virmos/fgpa_tetris/01_Hack1-minimal/ALU/ALU.png

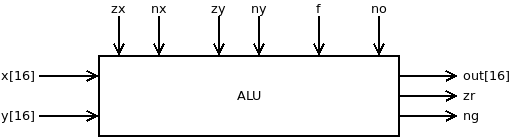
01_Hack1-minimal/ALU/ALU.png
