virmos/fgpa_tetris/01_Hack1-minimal/ALU/ALU_tb.png

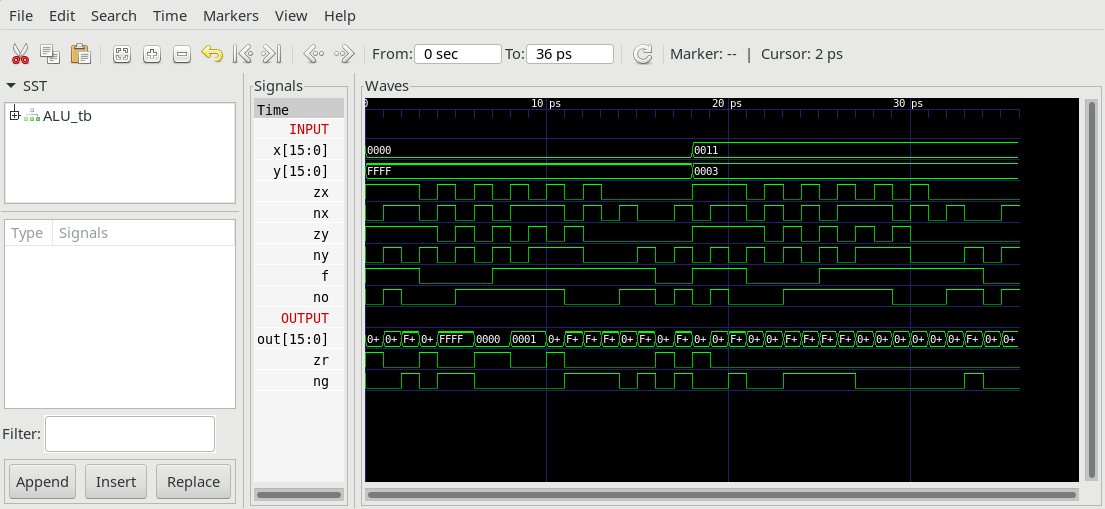
01_Hack1-minimal/ALU/ALU_tb.png
