virmos/fgpa_tetris/01_Hack1-minimal/Clock/Clock_tb.png

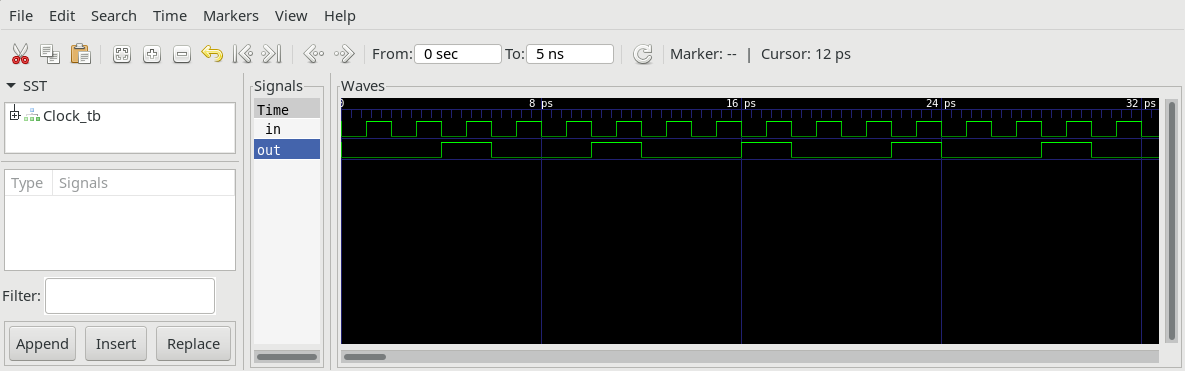
01_Hack1-minimal/Clock/Clock_tb.png
