virmos/fgpa_tetris/01_Hack1-minimal/CPU/CPU.png

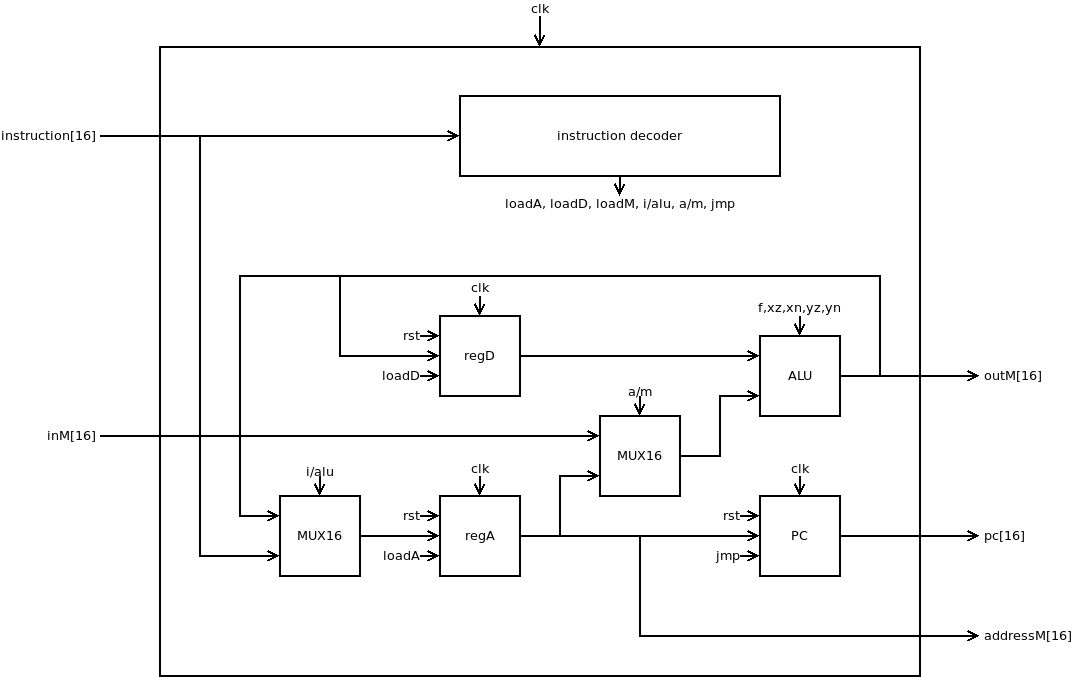
01_Hack1-minimal/CPU/CPU.png
