virmos/fgpa_tetris/01_Hack1-minimal/CPU/CPU_tb.png

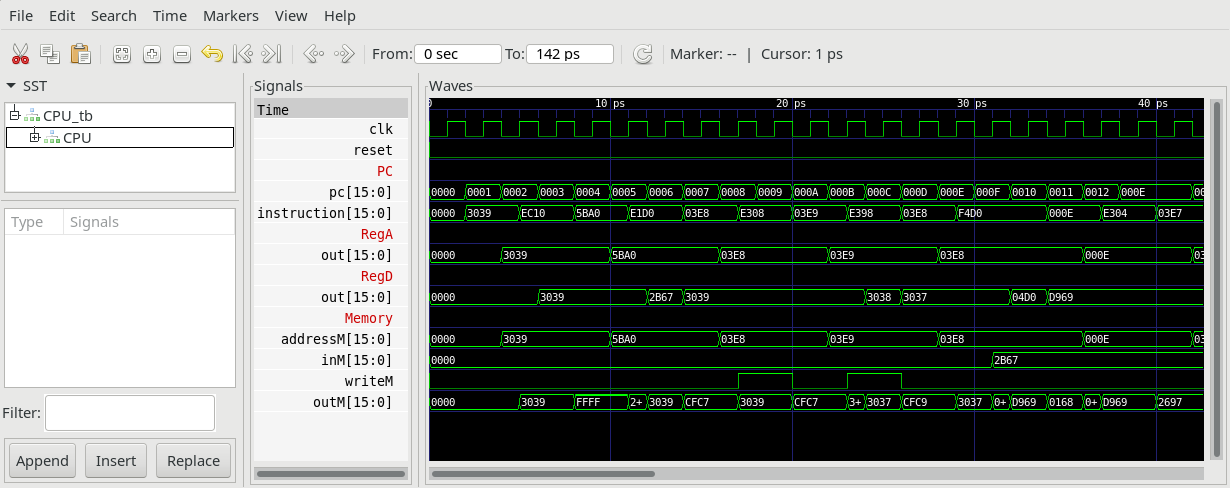
01_Hack1-minimal/CPU/CPU_tb.png
