virmos/fgpa_tetris/01_Hack1-minimal/Hack1/Hack1.png

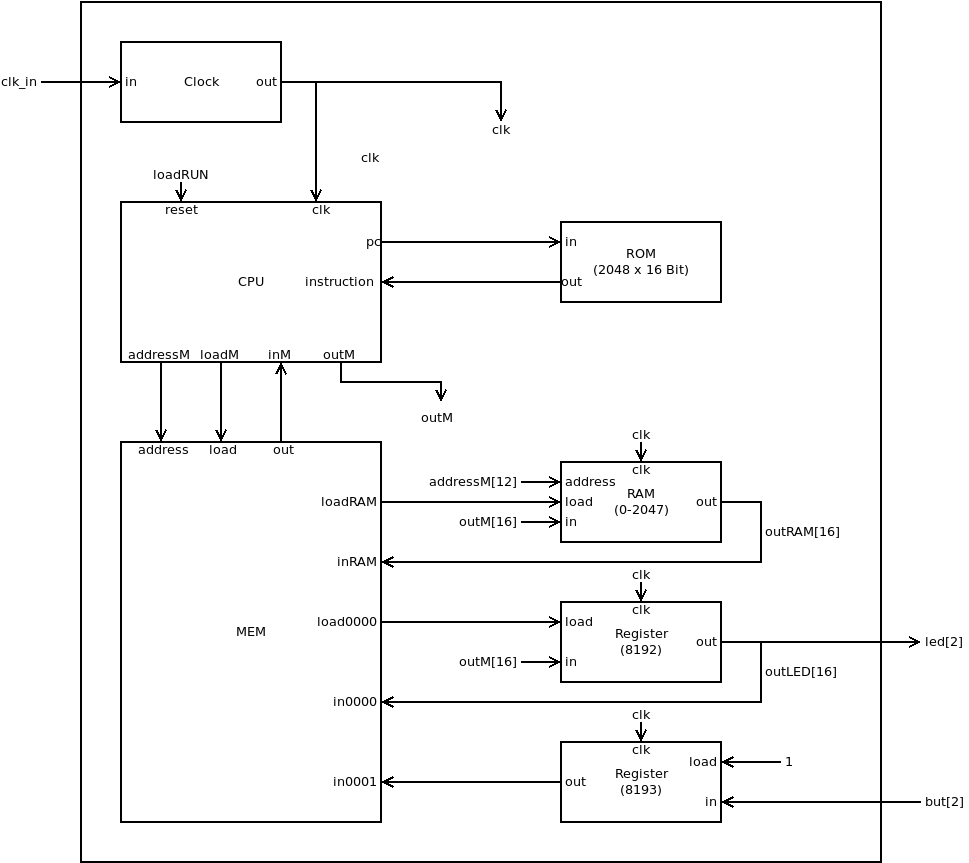
01_Hack1-minimal/Hack1/Hack1.png
