virmos/fgpa_tetris/01_Hack1-minimal/Hack1/Hack1_tb.png

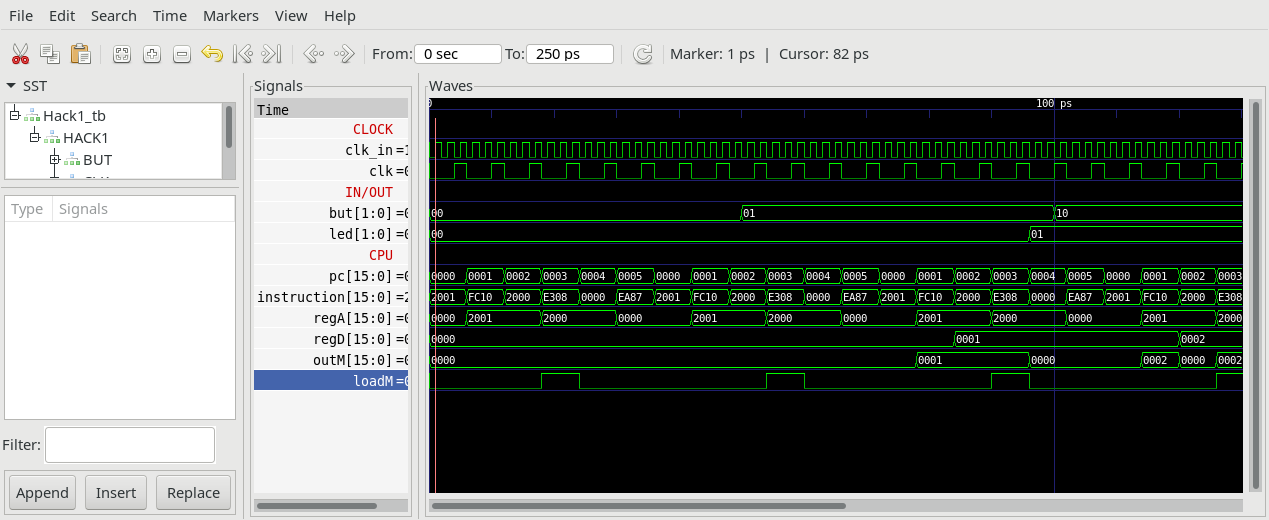
01_Hack1-minimal/Hack1/Hack1_tb.png
