virmos/fgpa_tetris/01_Hack1-minimal/Memory/Memory.png

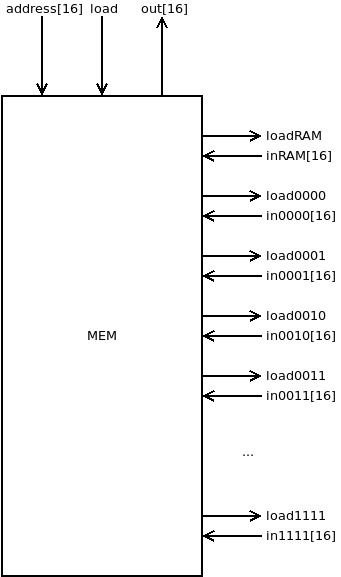
01_Hack1-minimal/Memory/Memory.png
