virmos/fgpa_tetris/01_Hack1-minimal/Memory/Memory_tb.png

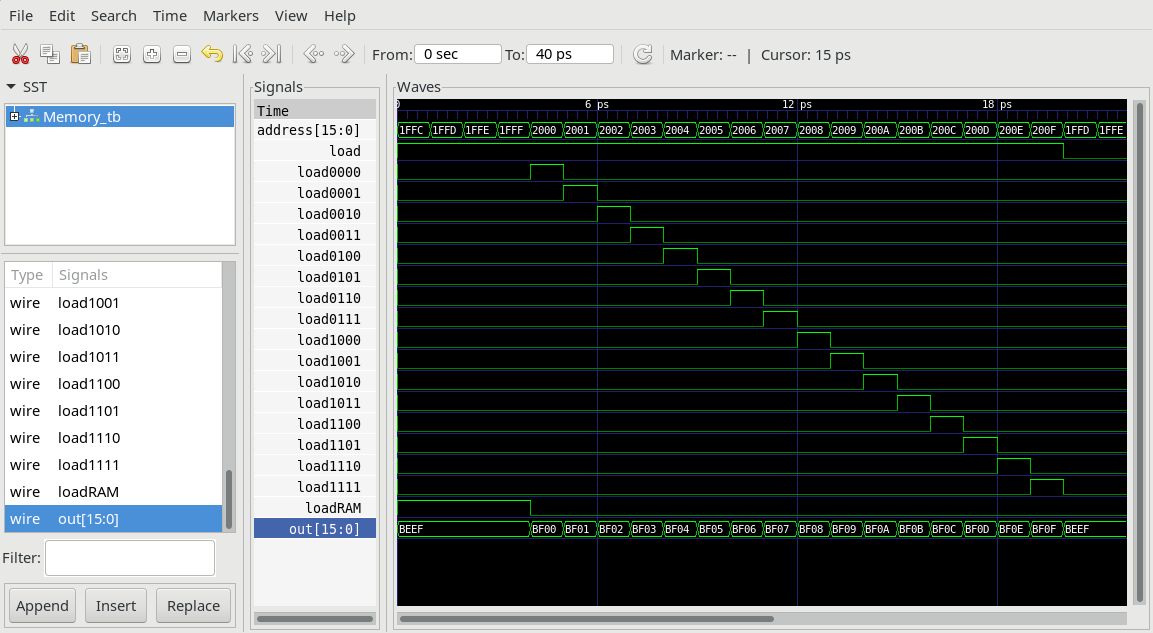
01_Hack1-minimal/Memory/Memory_tb.png
