virmos/fgpa_tetris/01_Hack1-minimal/PC/PC.png

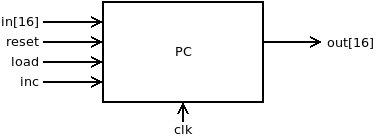
01_Hack1-minimal/PC/PC.png
