virmos/fgpa_tetris/01_Hack1-minimal/PC/PC_tb.png

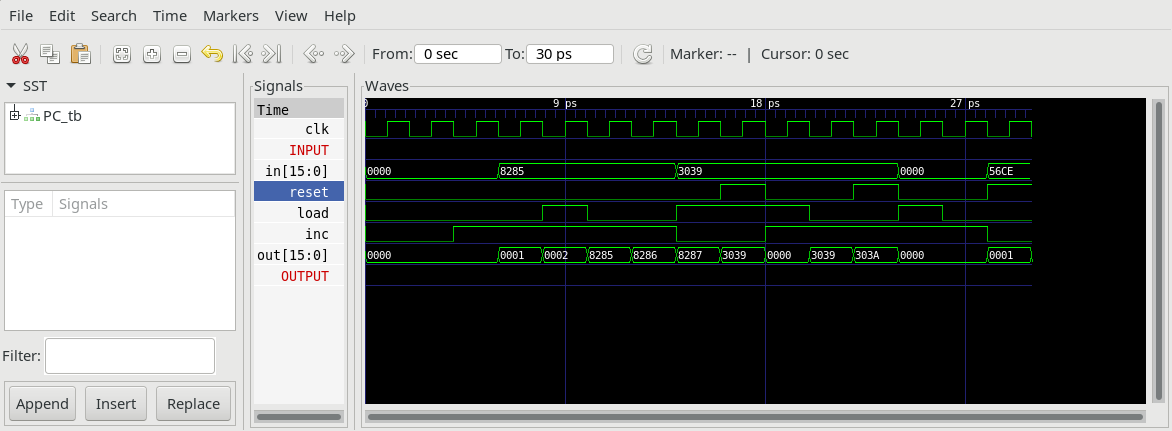
01_Hack1-minimal/PC/PC_tb.png
