virmos/fgpa_tetris/02_Hack2-UART/Hack2/Hack2_tb.png

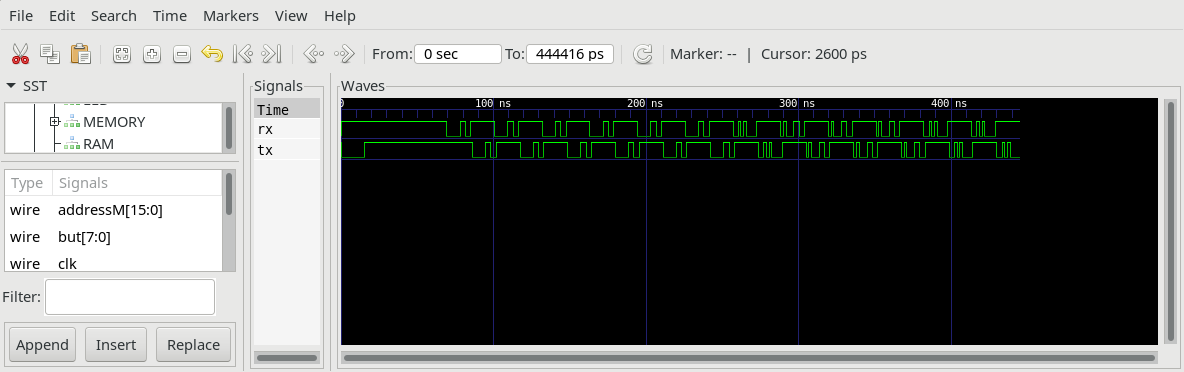
02_Hack2-UART/Hack2/Hack2_tb.png
