virmos/fgpa_tetris/02_Hack2-UART/ShifterR/ShifterR_tb.png

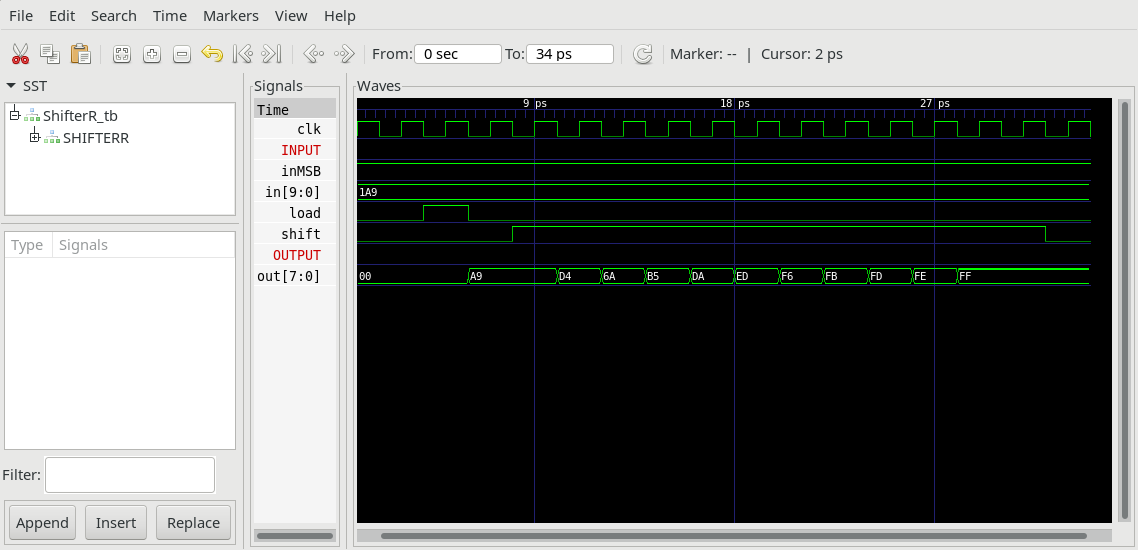
02_Hack2-UART/ShifterR/ShifterR_tb.png
