virmos/fgpa_tetris/02_Hack2-UART/Switch/Switch_tb.png

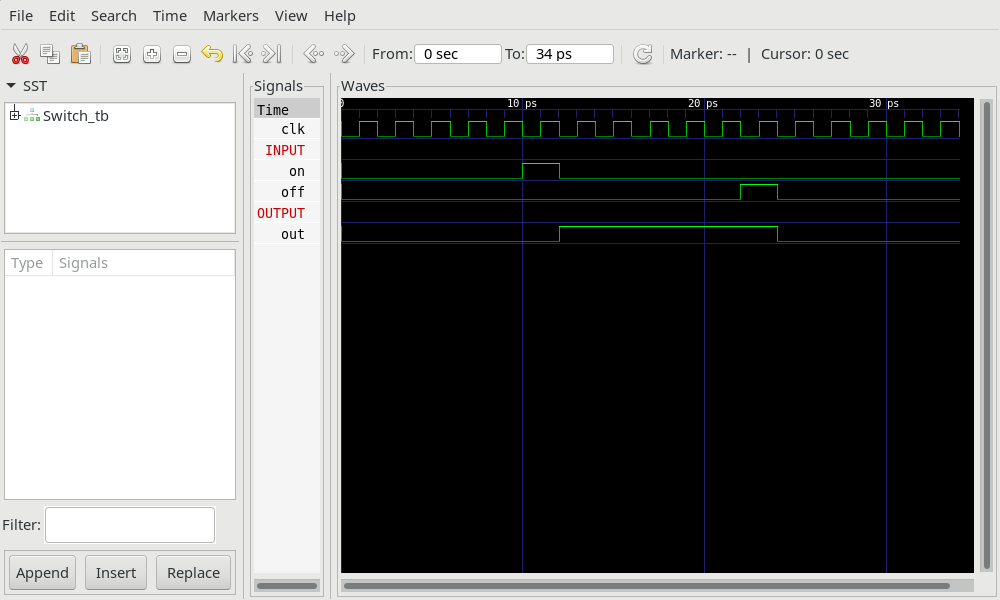
02_Hack2-UART/Switch/Switch_tb.png
