virmos/fgpa_tetris/02_Hack2-UART/UartRX/UartRX.png

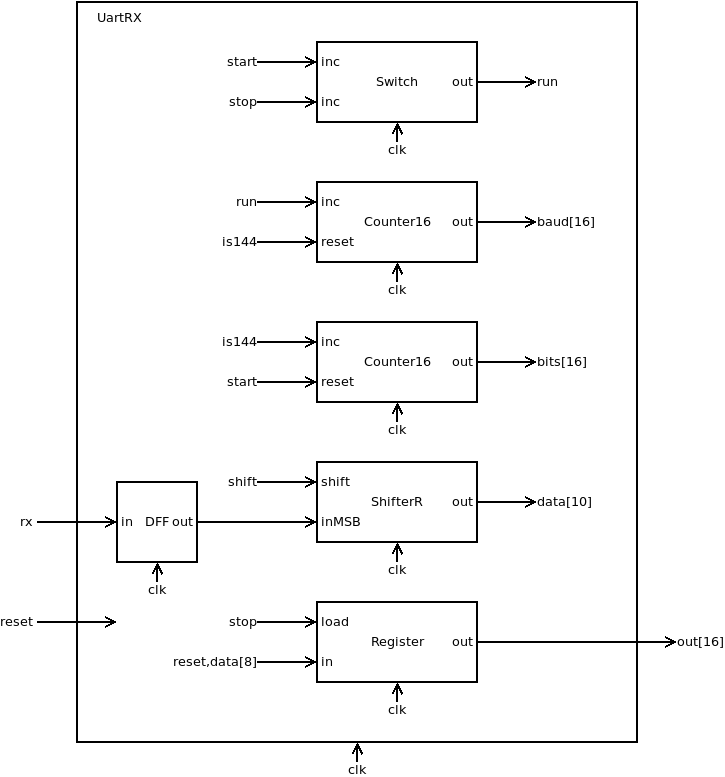
02_Hack2-UART/UartRX/UartRX.png
