virmos/fgpa_tetris/02_Hack2-UART/UartRX/UartRX_tb.png

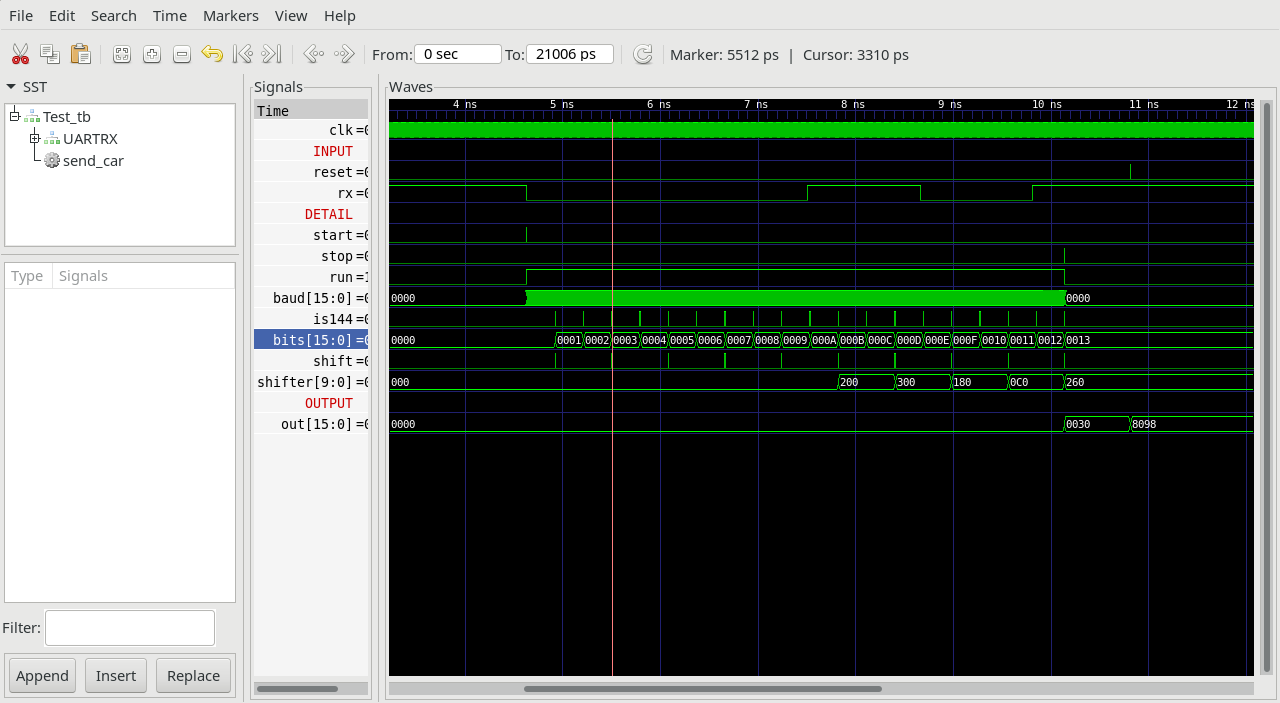
02_Hack2-UART/UartRX/UartRX_tb.png
