virmos/fgpa_tetris/02_Hack2-UART/UartTX/UartTX.png

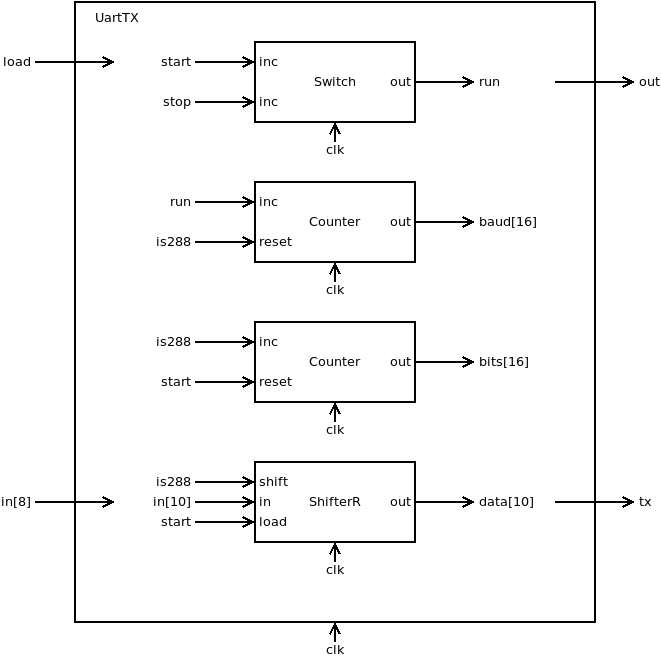
02_Hack2-UART/UartTX/UartTX.png
