virmos/fgpa_tetris/02_Hack2-UART/UartTX/UartTX_tb.png

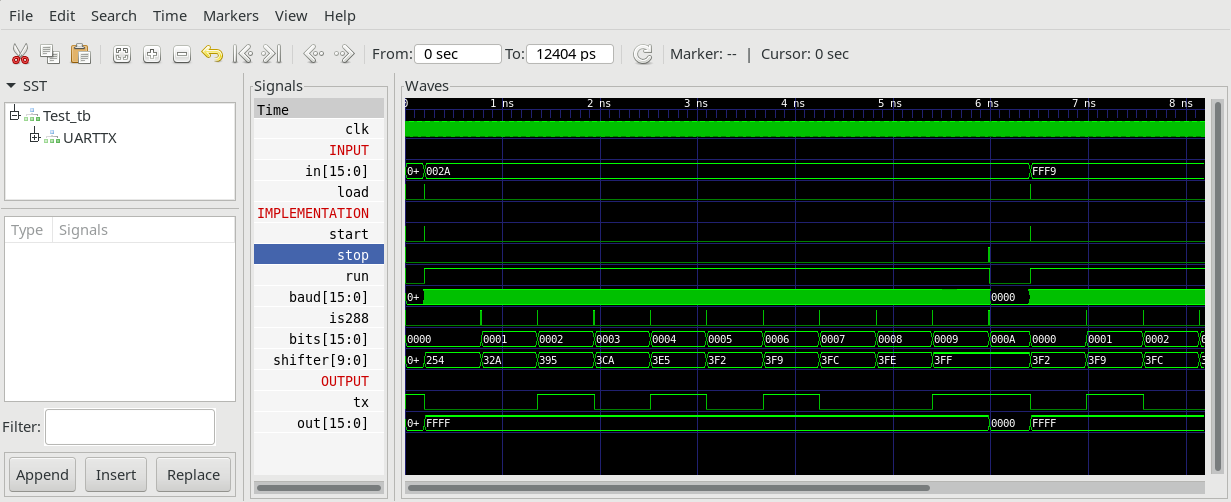
02_Hack2-UART/UartTX/UartTX_tb.png
