virmos/fgpa_tetris/03_Hack3-SRAM/Hack3/Hack3.png

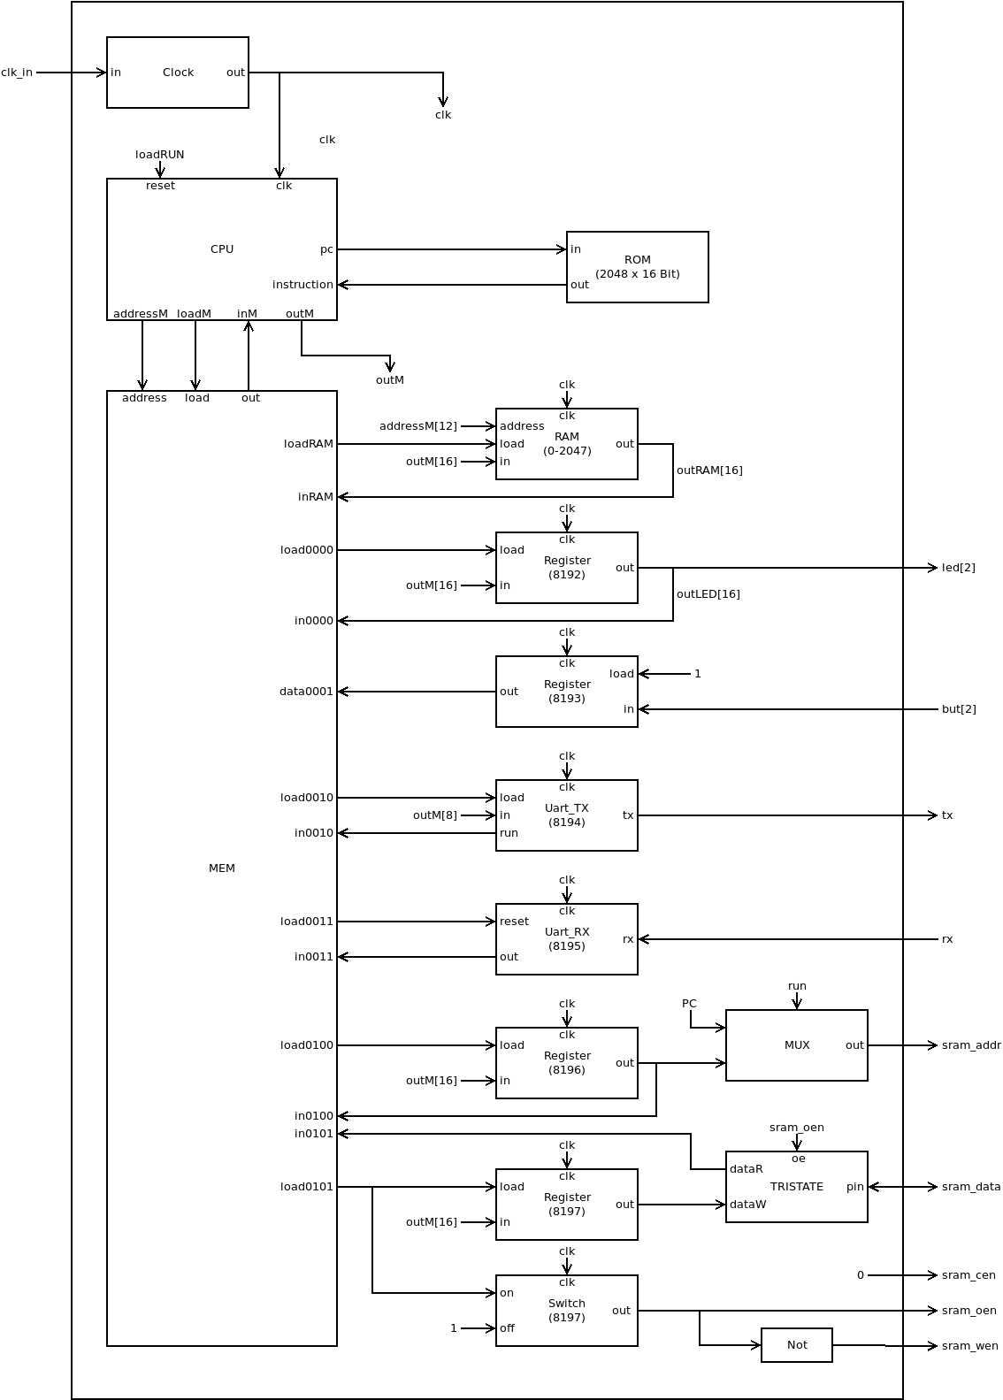
03_Hack3-SRAM/Hack3/Hack3.png
