virmos/fgpa_tetris/03_Hack3-SRAM/Hack3/Hack3_tb.png

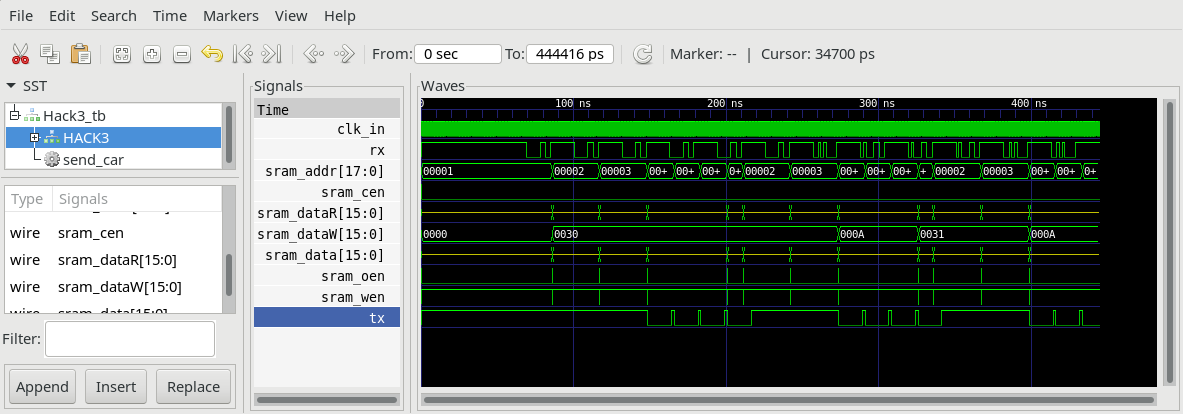
03_Hack3-SRAM/Hack3/Hack3_tb.png
