virmos/fgpa_tetris/04_Hack4-BOOT/doc/boot.png

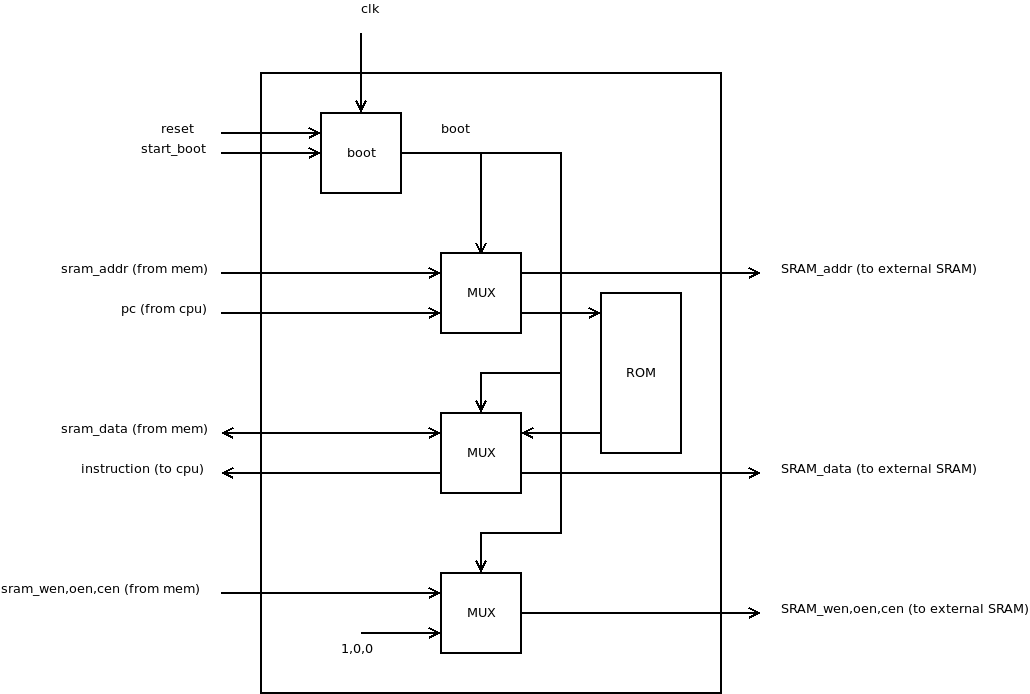
04_Hack4-BOOT/doc/boot.png
