virmos/fgpa_tetris/04_Hack4-BOOT/doc/bootloader.png

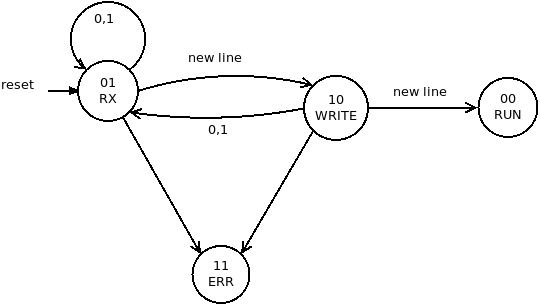
04_Hack4-BOOT/doc/bootloader.png
