virmos/fgpa_tetris/04_Hack4-BOOT/doc/hack-4.png

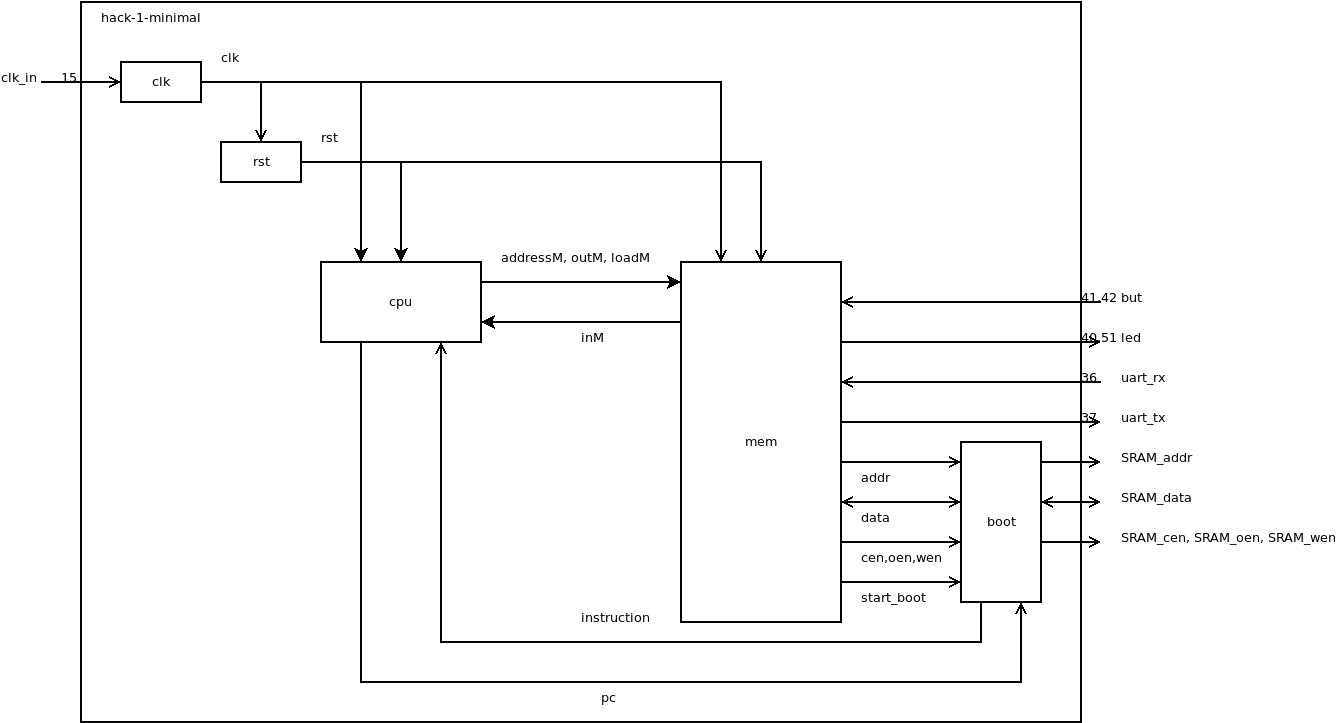
04_Hack4-BOOT/doc/hack-4.png
