virmos/fgpa_tetris/04_Hack4-BOOT/Hack4/Hack4.png

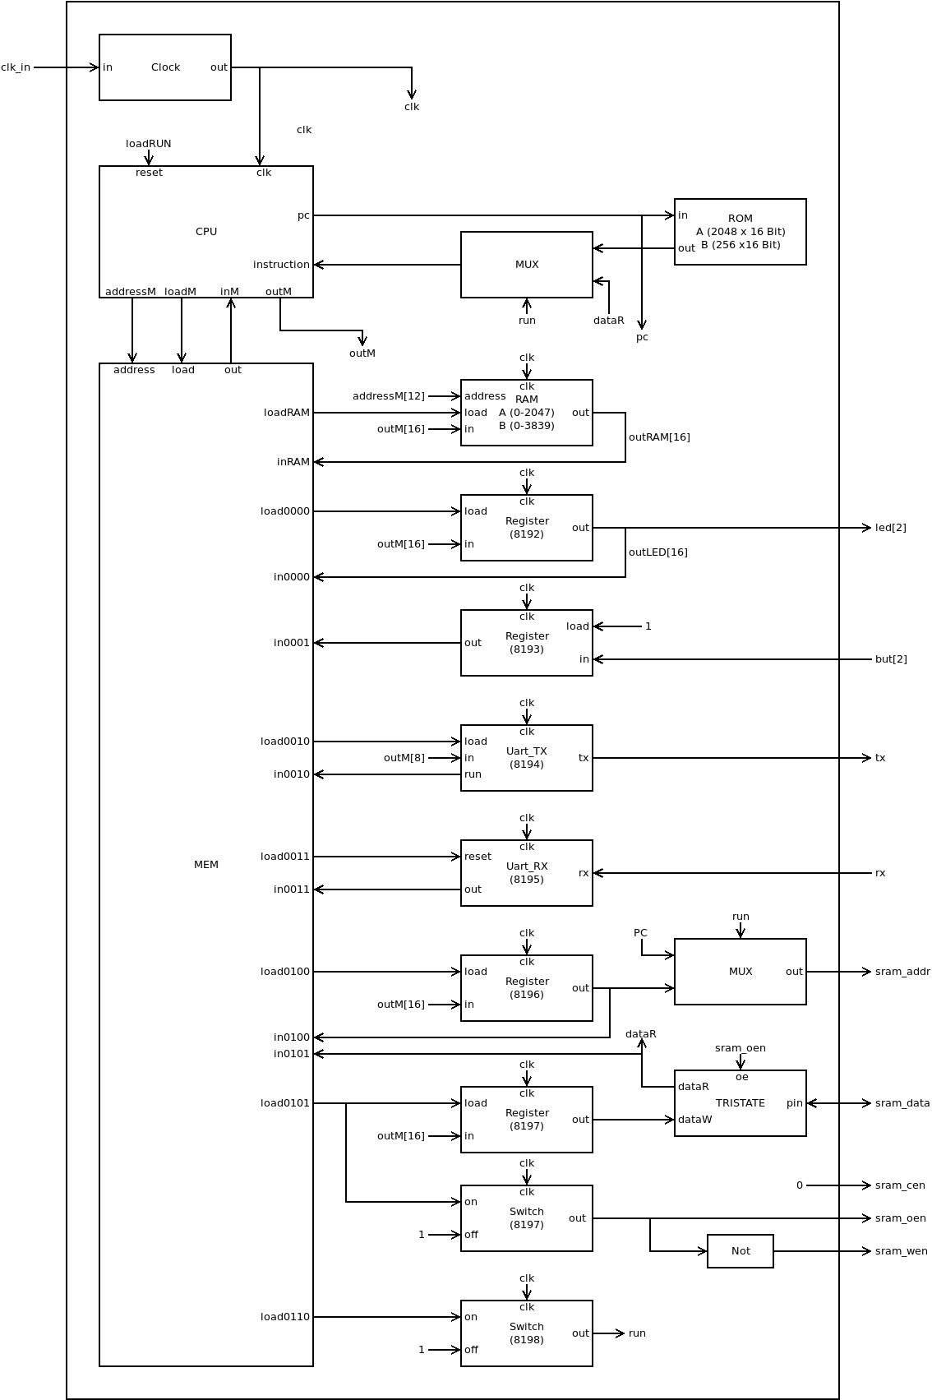
04_Hack4-BOOT/Hack4/Hack4.png
