virmos/fgpa_tetris/05_Jack-OS/Average/average.JPG

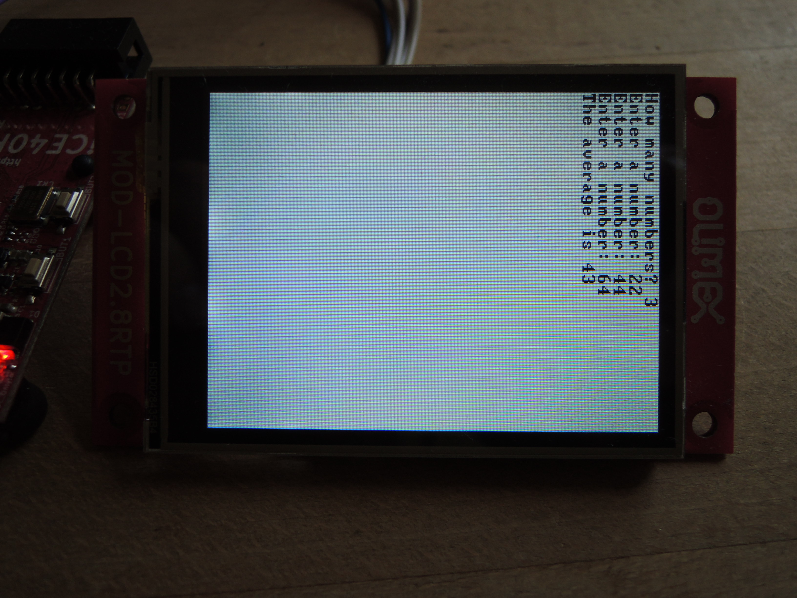
05_Jack-OS/Average/average.JPG
