virmos/fgpa_tetris/06_Hack6-LCD/Hack6/Hack6_tb.png

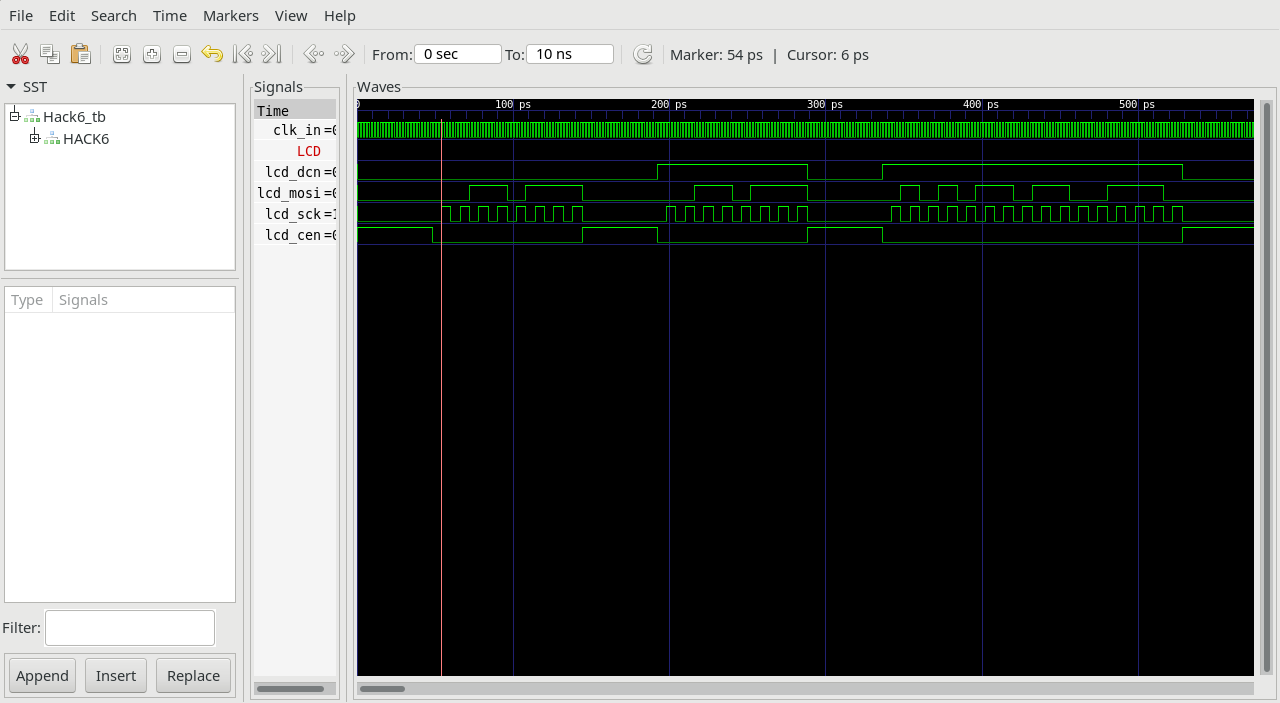
06_Hack6-LCD/Hack6/Hack6_tb.png
