virmos/fgpa_tetris/06_Hack6-LCD/Hack6/Hack.png

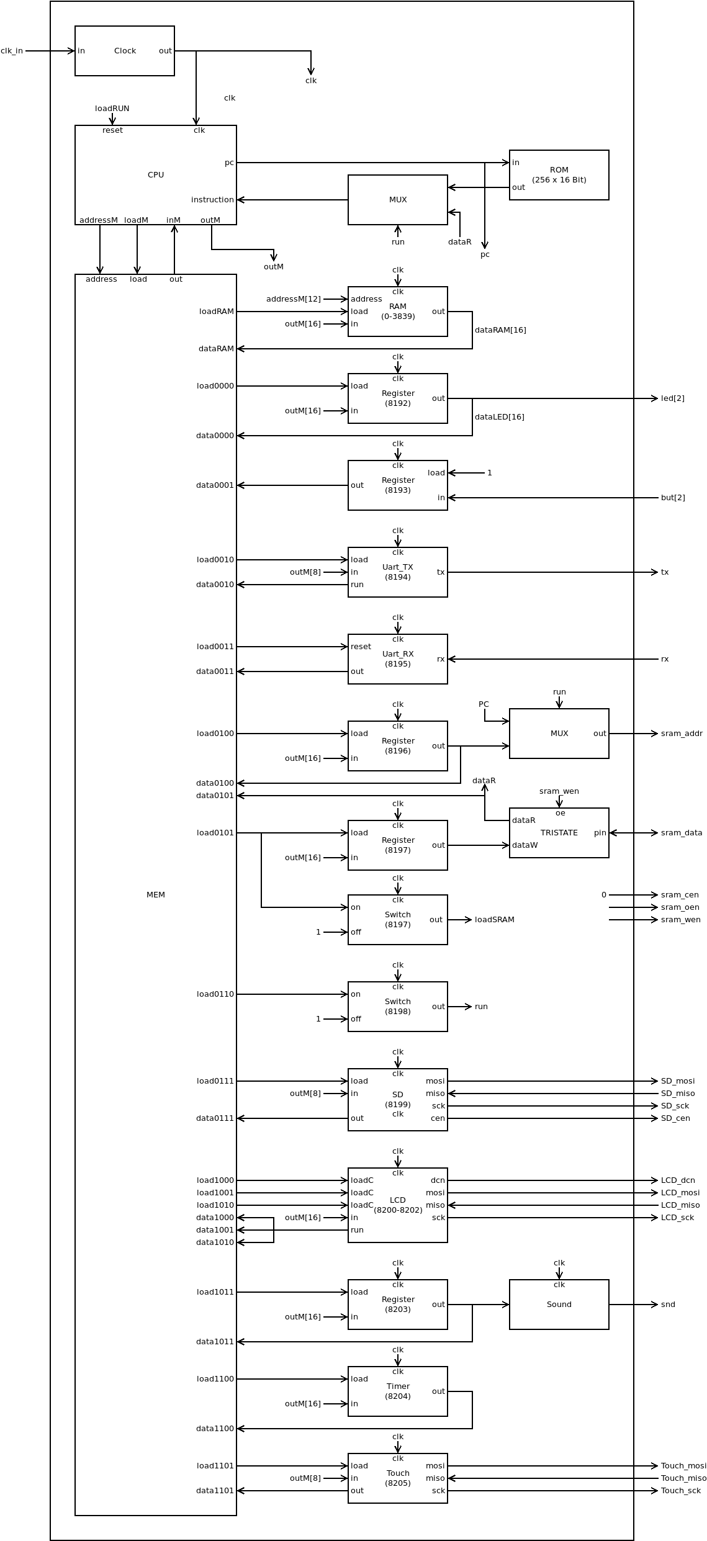
06_Hack6-LCD/Hack6/Hack.png
