virmos/fgpa_tetris/06_Hack6-LCD/jack/Pong/pong.jpg

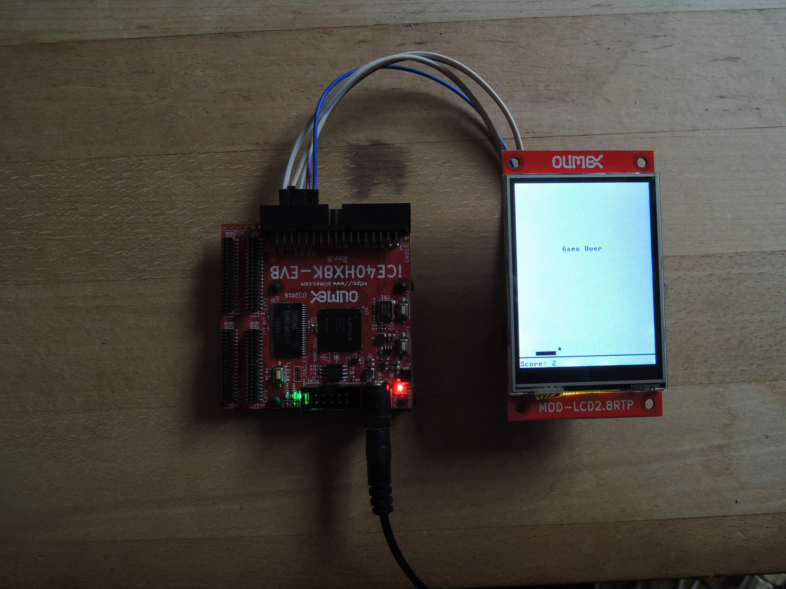
06_Hack6-LCD/jack/Pong/pong.jpg
