virmos/fgpa_tetris/06_Hack6-LCD/LCD/LCD.png

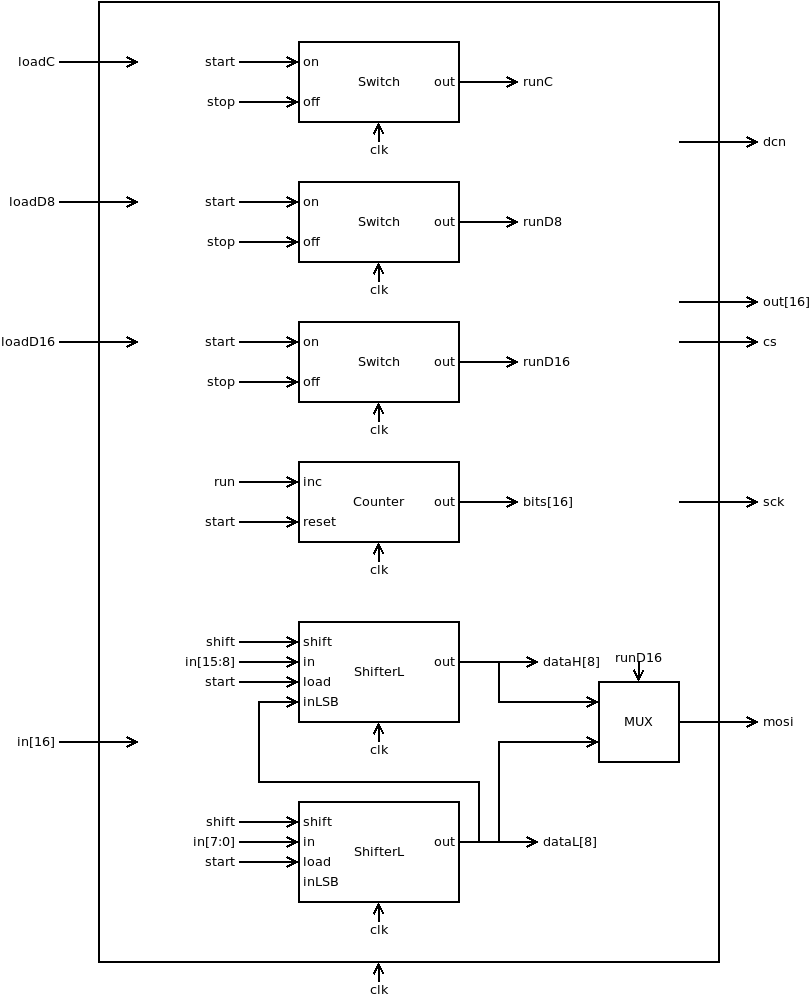
06_Hack6-LCD/LCD/LCD.png
