virmos/fgpa_tetris/06_Hack6-LCD/LCD/LCD_tb.png

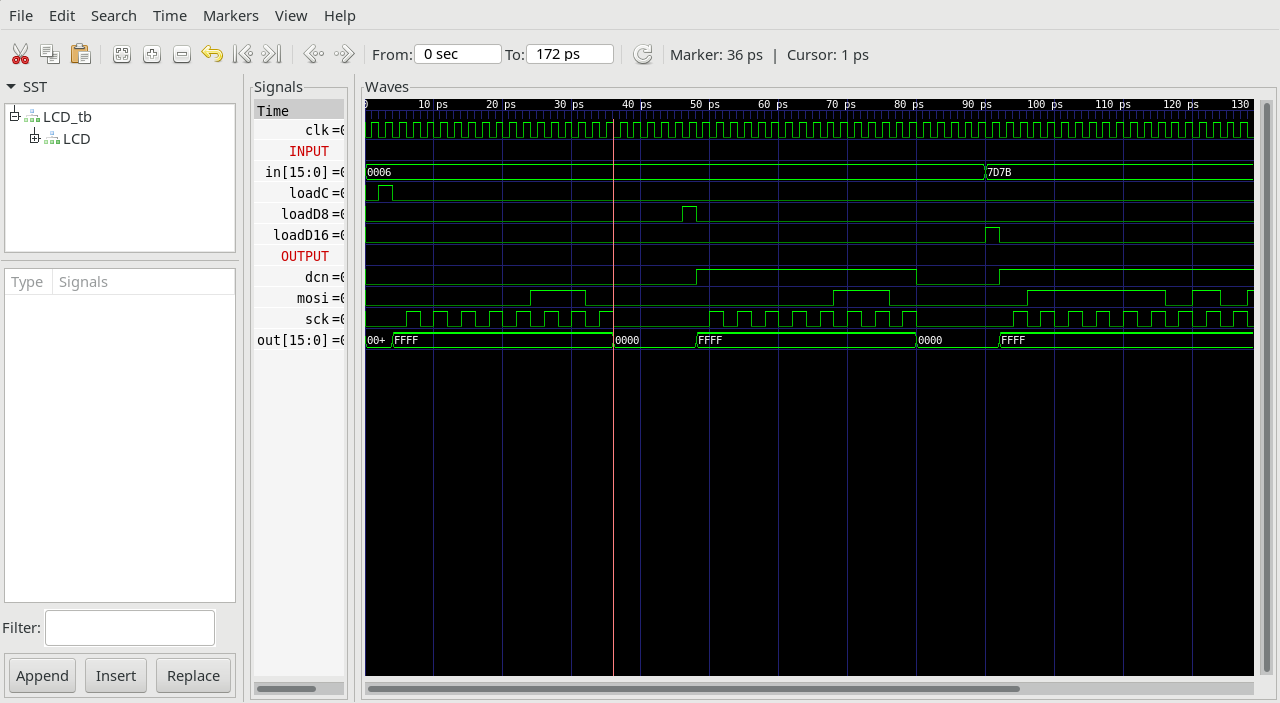
06_Hack6-LCD/LCD/LCD_tb.png
