virmos/fgpa_tetris/06_Hack6-LCD/ShifterL/ShifterL_tb.png

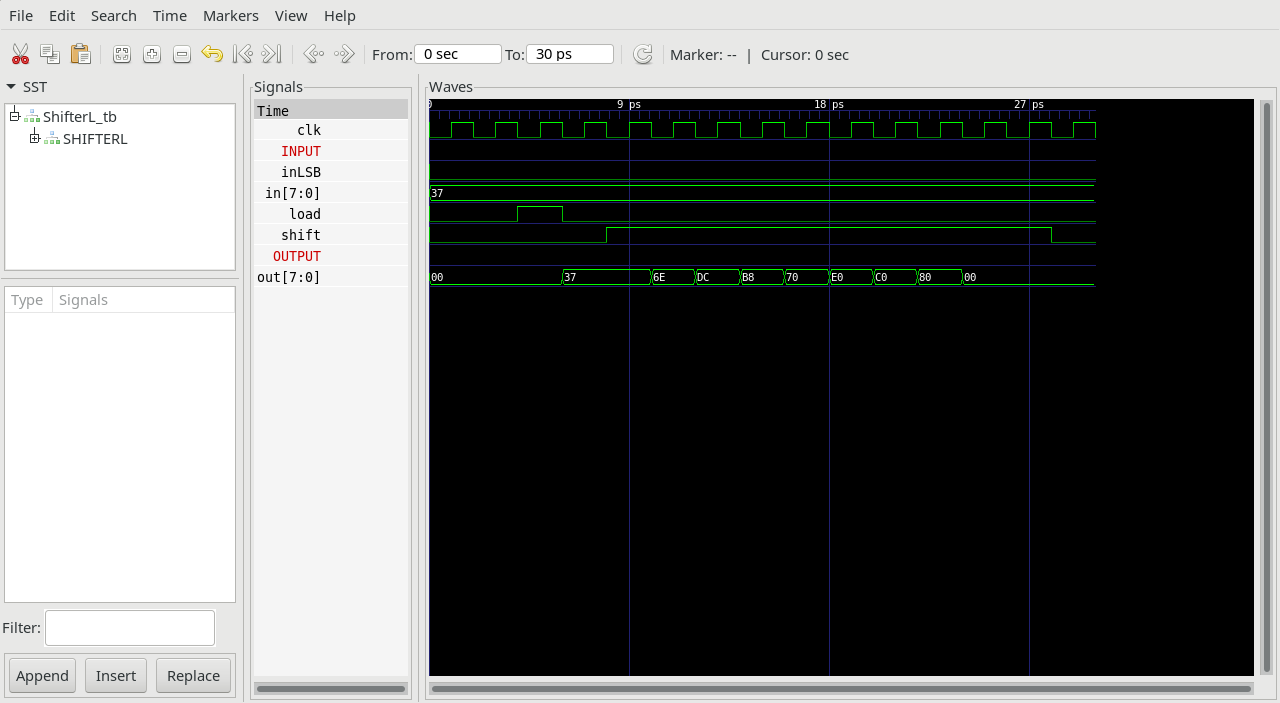
06_Hack6-LCD/ShifterL/ShifterL_tb.png
