virmos/fgpa_tetris/07_Hack7-Touch/Hack7/Hack7.png

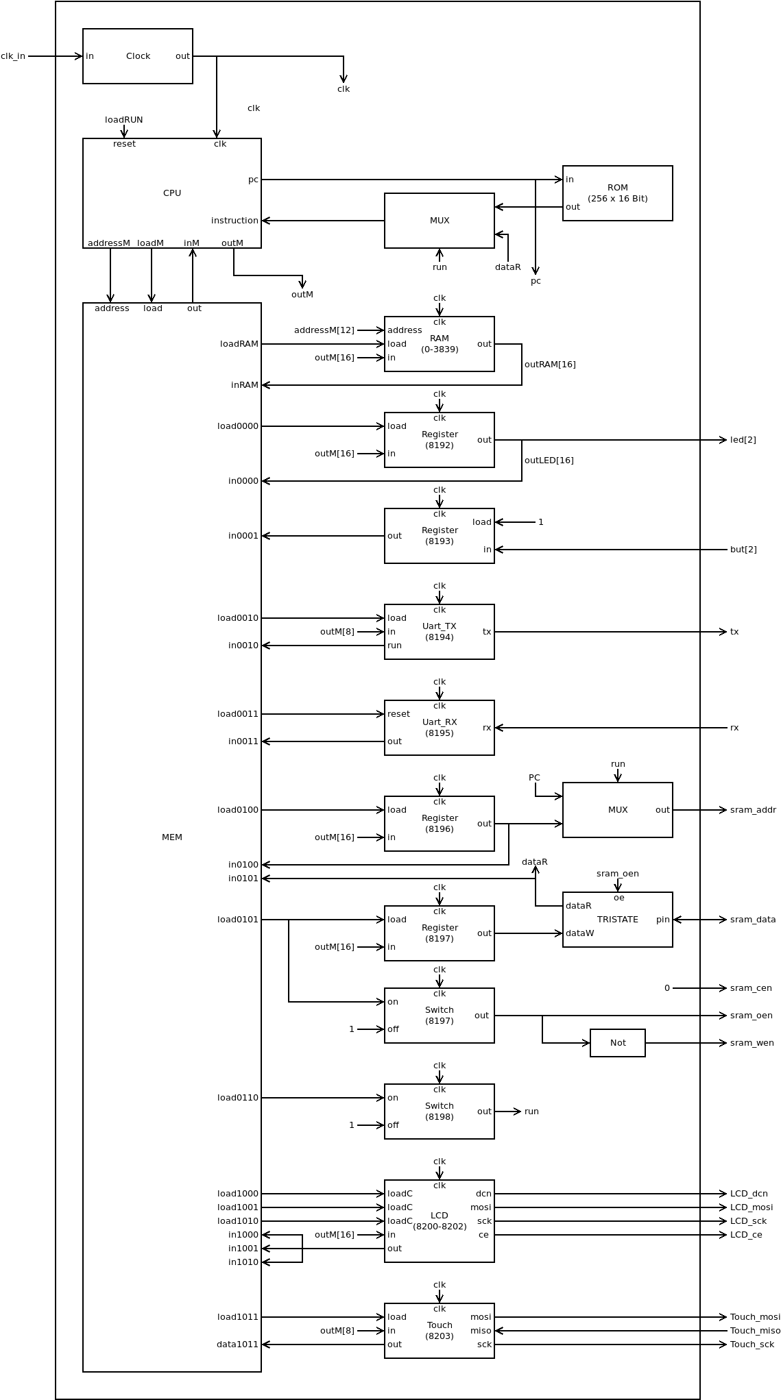
07_Hack7-Touch/Hack7/Hack7.png
