virmos/fgpa_tetris/07_Hack7-Touch/TouchJumper.JPG

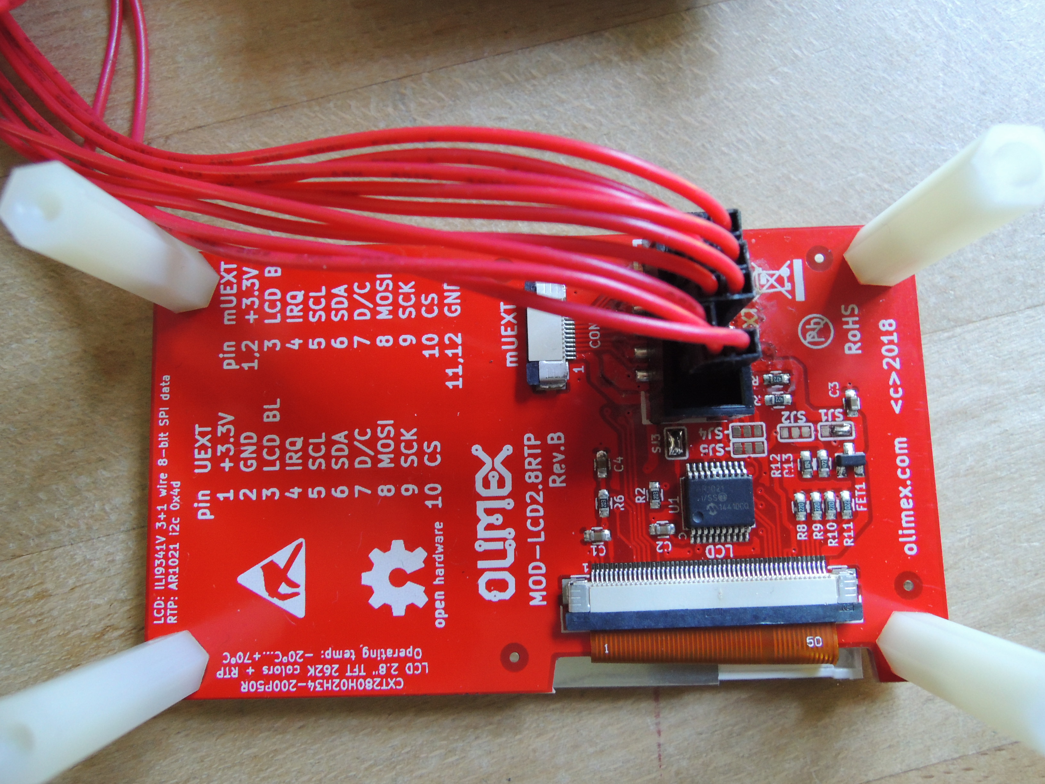
07_Hack7-Touch/TouchJumper.JPG
