virmos/fgpa_tetris/08_Hack8-Sound/Hack8/Hack8.png

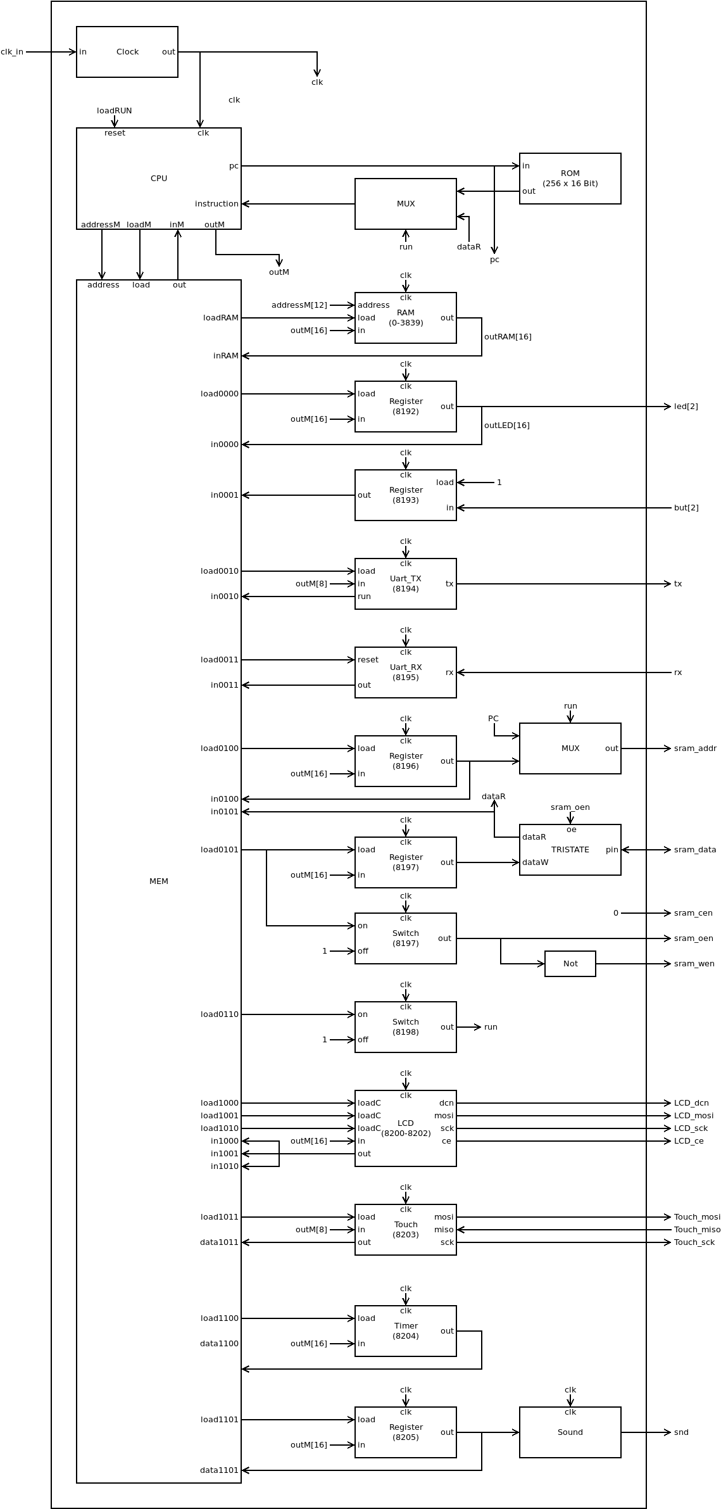
08_Hack8-Sound/Hack8/Hack8.png
