virmos/fgpa_tetris/08_Hack8-Sound/Hack8/Hack8_tb.png

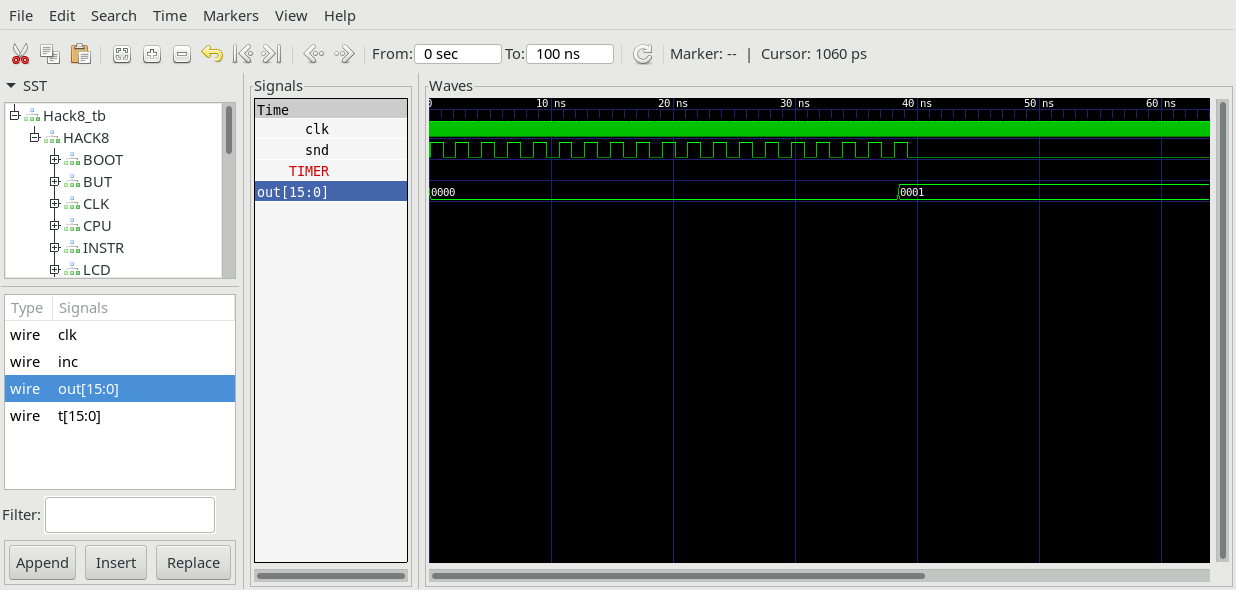
08_Hack8-Sound/Hack8/Hack8_tb.png
