virmos/fgpa_tetris/08_Hack8-Sound/Sound/Sound_tb.png

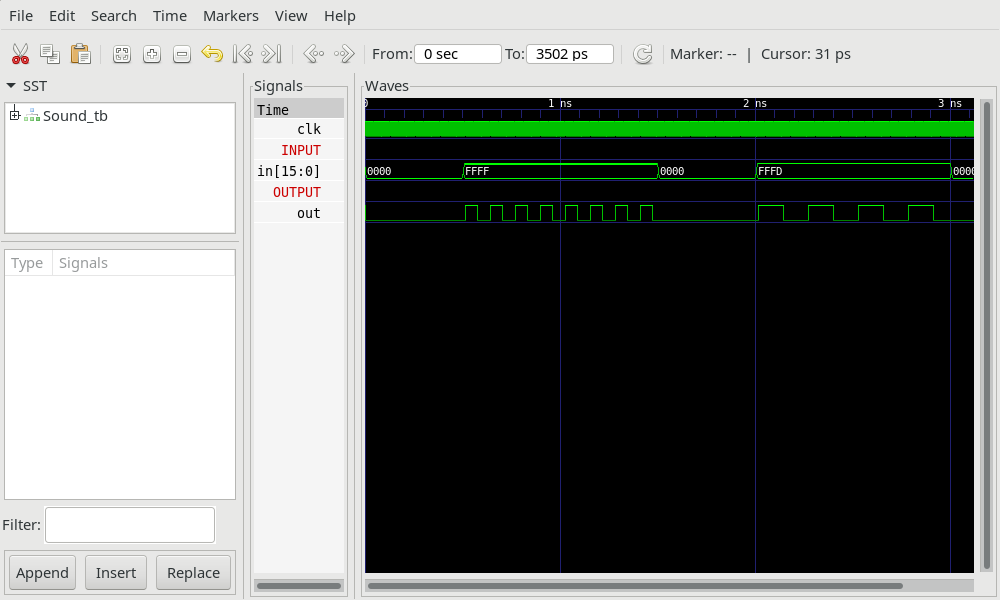
08_Hack8-Sound/Sound/Sound_tb.png
