virmos/fgpa_tetris/08_Hack8-Sound/Timer/Timer_tb.png

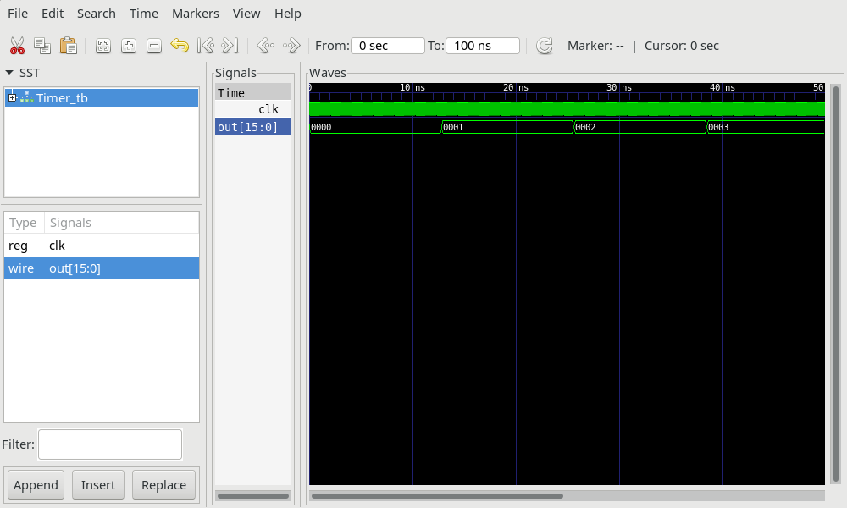
08_Hack8-Sound/Timer/Timer_tb.png
