virmos/fgpa_tetris/09_Hack9-SD/Hack9/Hack9_tb.png

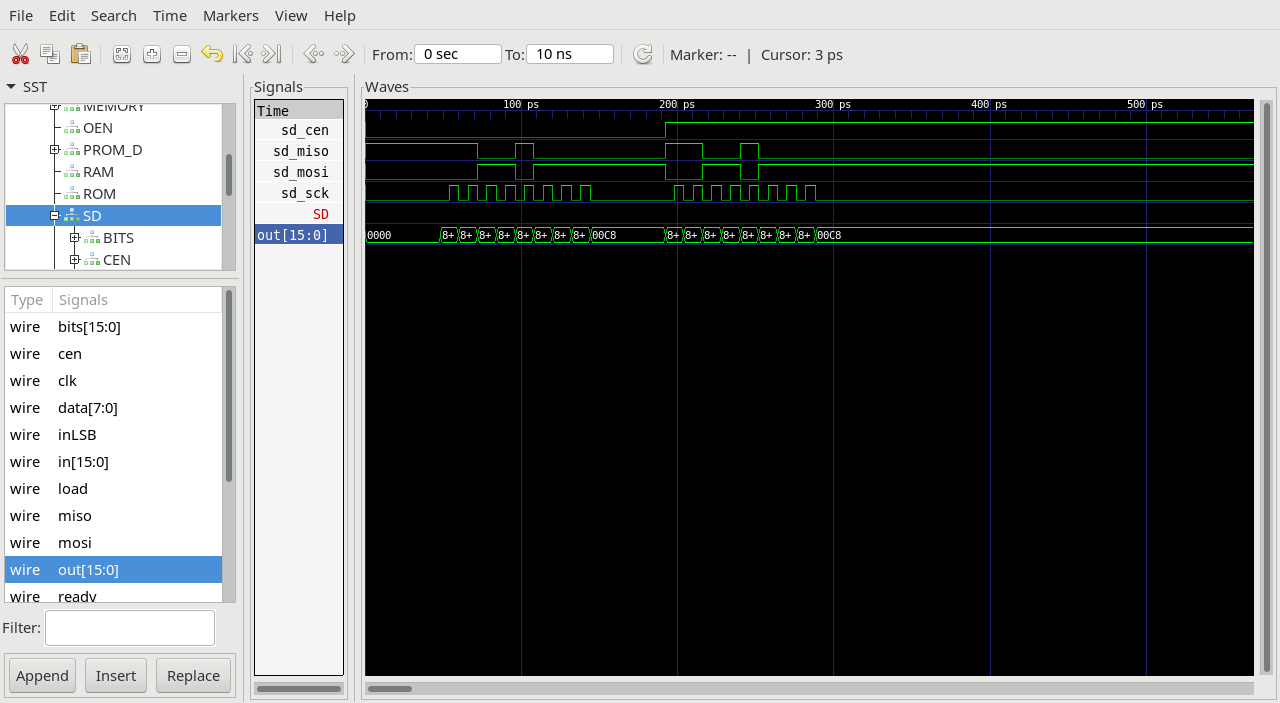
09_Hack9-SD/Hack9/Hack9_tb.png
