virmos/fgpa_tetris/09_Hack9-SD/SD/SD.png

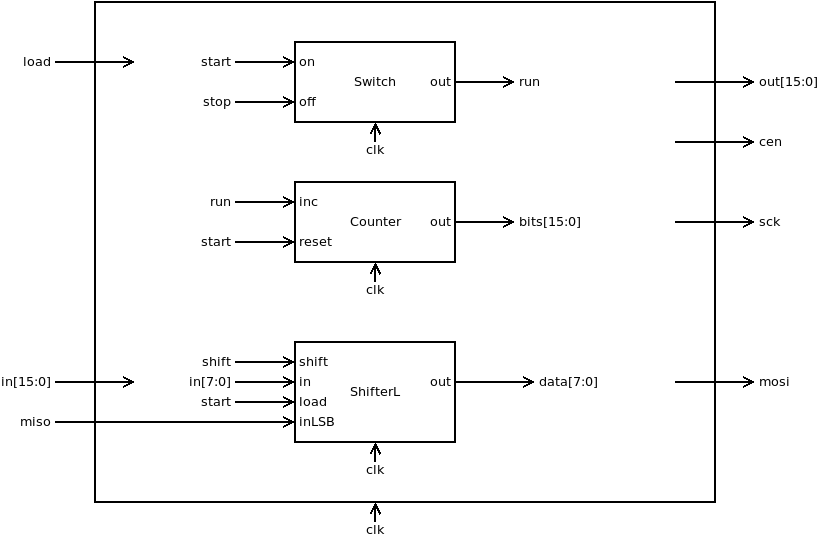
09_Hack9-SD/SD/SD.png
