virmos/fgpa_tetris/09_Hack9-SD/SD/SD_tb.png

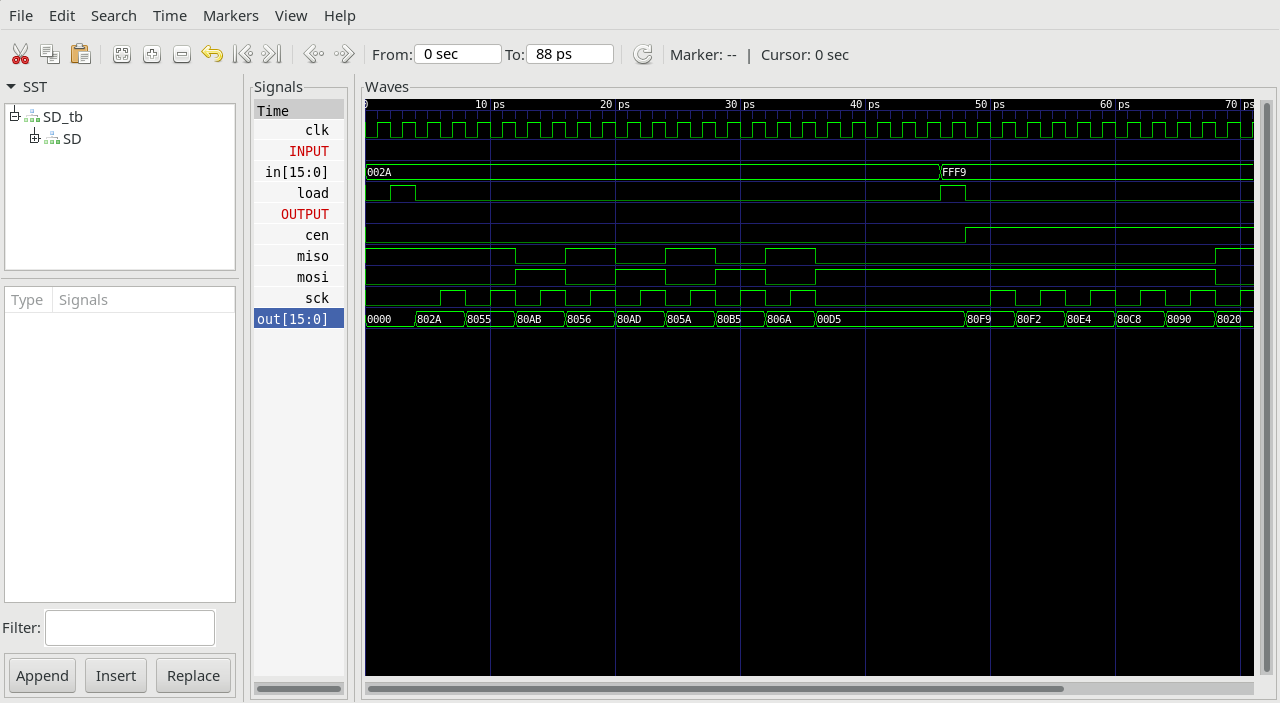
09_Hack9-SD/SD/SD_tb.png
