virmos/fgpa_tetris/10_Hack10-Network/jack/Network_new.png

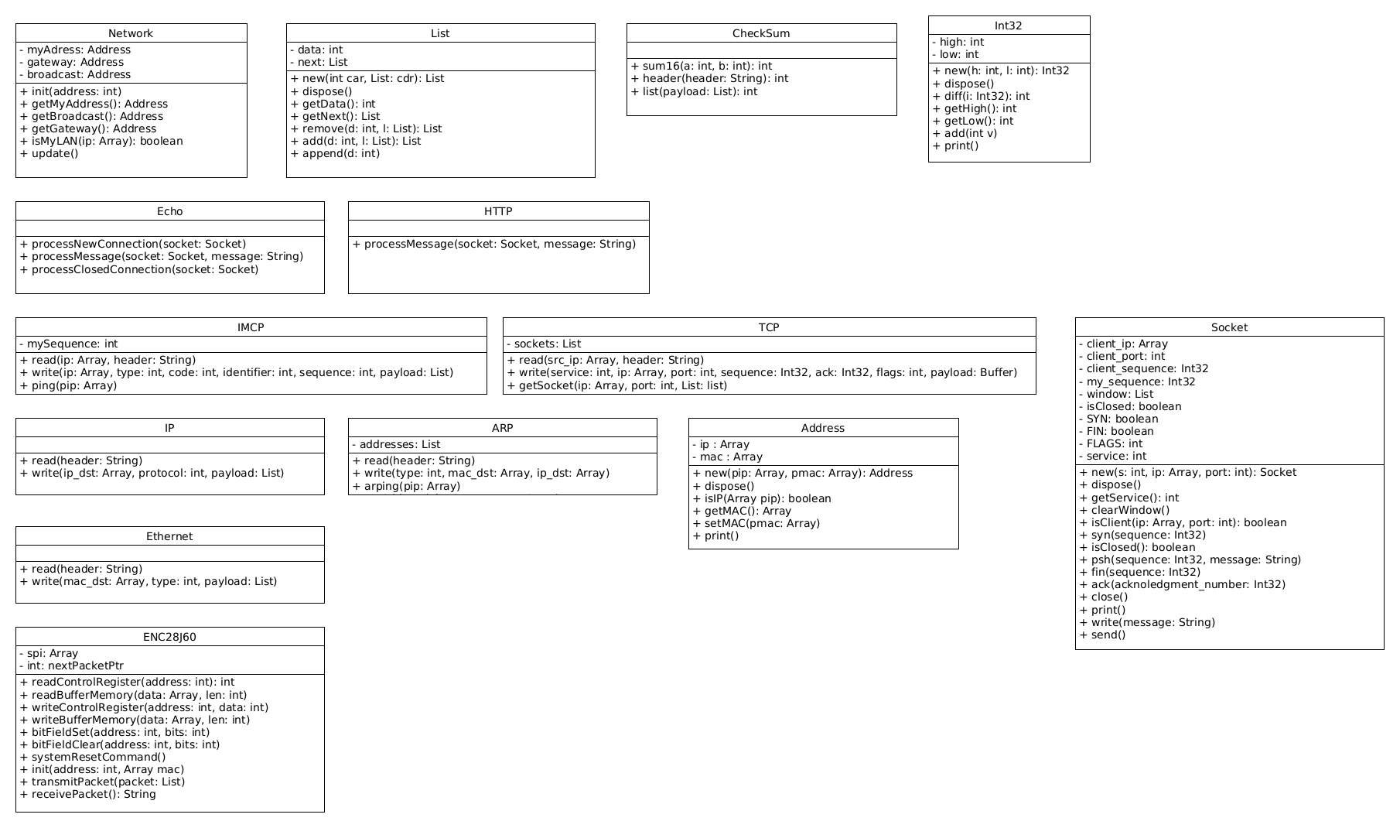
10_Hack10-Network/jack/Network_new.png
