virmos/fgpa_tetris/11_Cube/pics/cube_front.jpg

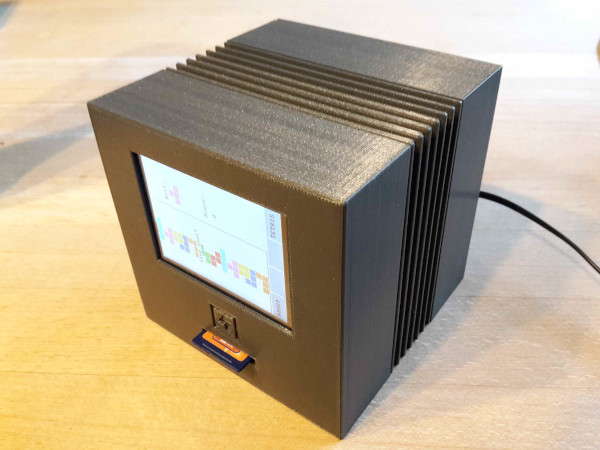
11_Cube/pics/cube_front.jpg
