virmos/fgpa_tetris/11_Cube/pics/cube_inside.jpg

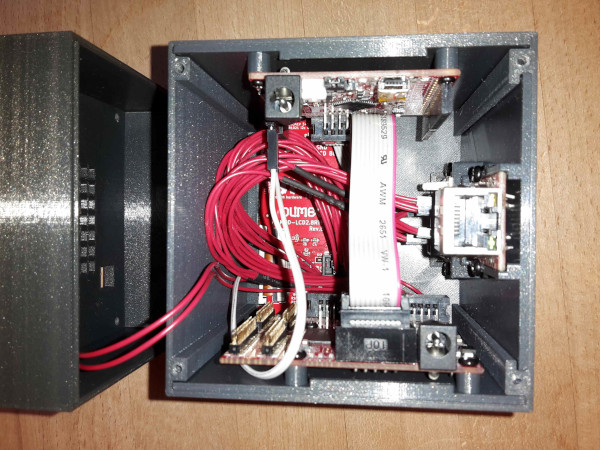
11_Cube/pics/cube_inside.jpg
