virmos/fgpa_tetris/11_Cube/pics/cube_rear.jpg

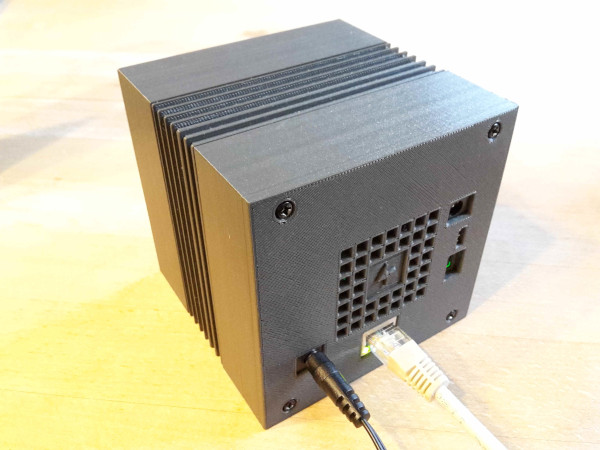
11_Cube/pics/cube_rear.jpg
