virmos/fgpa_tetris/datasheets/iCE40HX8K-EVB-1.jpg

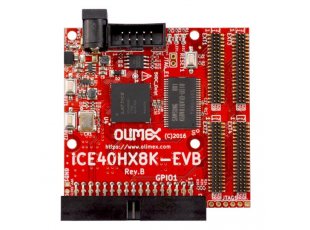
datasheets/iCE40HX8K-EVB-1.jpg
