virmos/fgpa_tetris/datasheets/kl10.gif

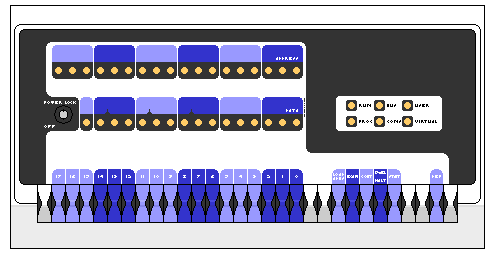
datasheets/kl10.gif
