virmos/fgpa_tetris/00_Requirement/doc/BOM.png

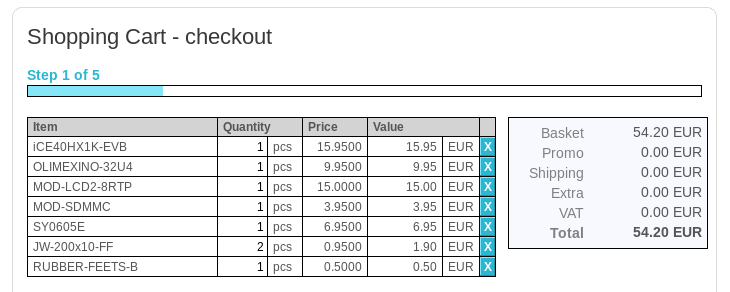
00_Requirement/doc/BOM.png
