virmos/fgpa_tetris/06_Hack6-LCD/jack/OutputTest/OutputTestOutput.gif

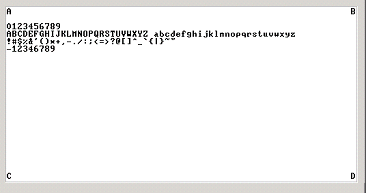
06_Hack6-LCD/jack/OutputTest/OutputTestOutput.gif
