virmos/fgpa_tetris/06_Hack6-LCD/jack/ScreenTest/screen.jpg

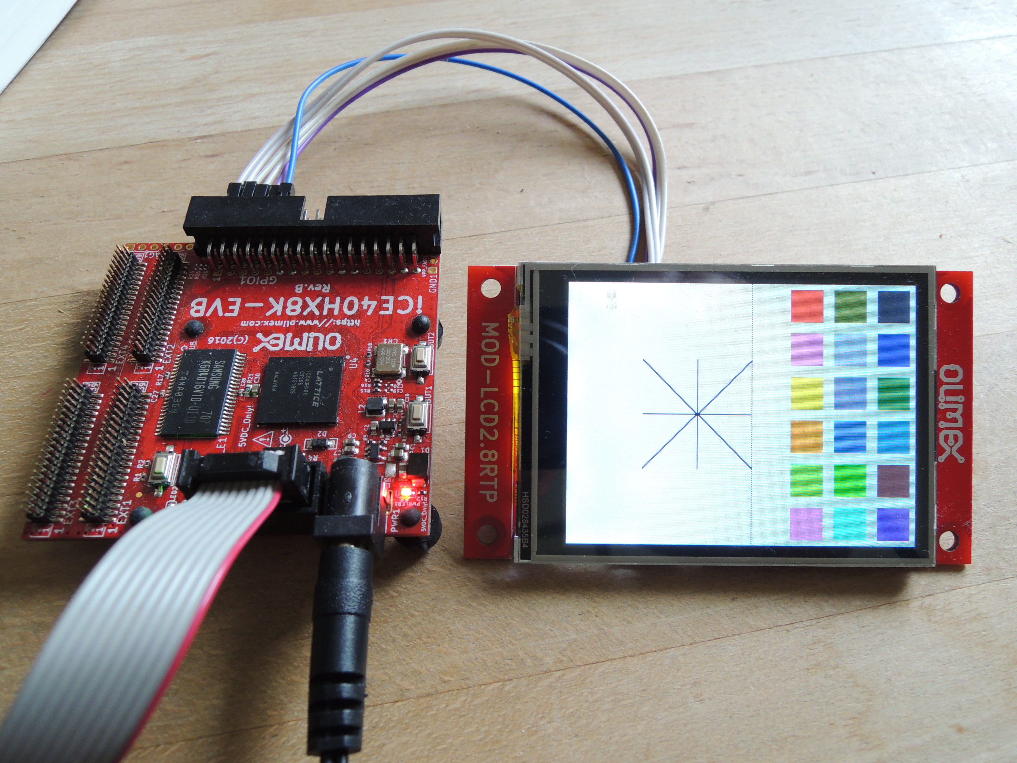
06_Hack6-LCD/jack/ScreenTest/screen.jpg
