virmos/fgpa_tetris/08_Hack8-Sound/jack/SoundTest/SDTest.jpg

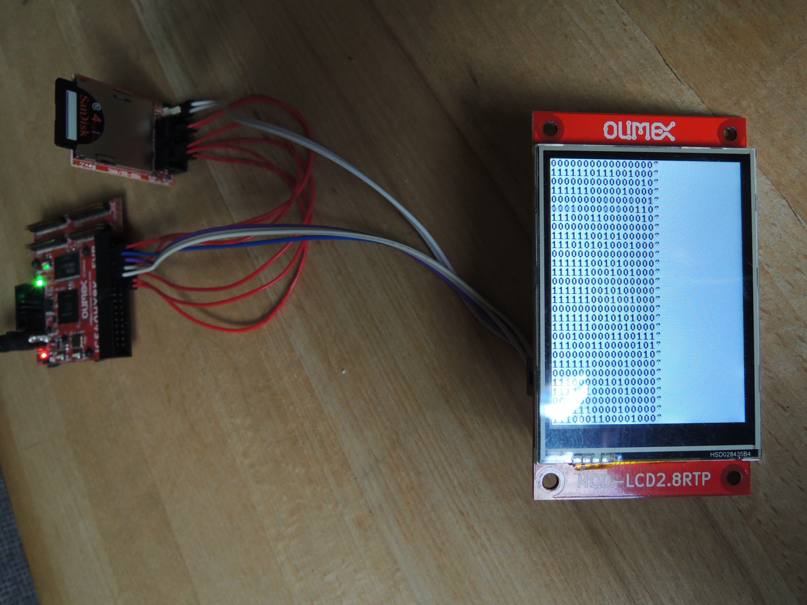
08_Hack8-Sound/jack/SoundTest/SDTest.jpg
