virmos/fgpa_tetris/08_Hack8-Sound/Timer/Timer_tb.v

module Timer_tb();

reg clk = 0;
wire [15:0] out;

Timer
  TIMER(
	.clk(clk),
	.out(out)
  );

always #1 clk = ~clk;

initial begin
  $dumpfile("Timer_tb.vcd");
  $dumpvars(0, Timer_tb);
	# 100000
  $finish;
end

endmodule
