virmos/fgpa_tetris/Hack/DFF.v

/**
* Data-Flip-Flop
* out[t+1] = in[t]
*
* This module is implemented using reg-variables in verilog
*/

`default_nettype none
module DFF(
		input wire clk,
		input wire in,
		output out
);
	reg out;
	always @(posedge clk)
		if (in) out <= 1'b1;
		else out <= 1'b0;

endmodule
