virmos/fgpa_tetris/Hack/DMux4Way.v

/**
 * 4-way demultiplexor:
 * {a, b, c, d} = {in, 0, 0, 0} if sel == 00
 *                {0, in, 0, 0} if sel == 01
 *                {0, 0, in, 0} if sel == 10
 *                {0, 0, 0, in} if sel == 11
 */

module DMux4Way(
	input wire in,
	input wire [1:0] sel,
    output wire a,
	output wire b,
	output wire c,
	output wire d
	);
// your implementation comes here:




endmodule
