virmos/fgpa_tetris/Hack/FullAdder.v

/**
 * Computes the sum of three bits.
 */
`default_nettype none

module FullAdder(
	input wire a,		//1-bit input
	input wire b,		//1-bit input
	input wire c,		//1-bit input
	output wire sum,	//Right bit of a + b + c
	output wire carry	//Left bit of a + b + c
);
// your implementation comes here:




endmodule
