virmos/fgpa_tetris/Hack/Inc16.v

/**
 * 16-bit incrementer:
 * out = in + 1 (arithmetic addition)
 */
`default_nettype none

module Inc16(
	input wire [15:0] in,
	output wire [15:0] out
);

// your implementation comes here:



endmodule
