virmos/fgpa_tetris/Hack/Mux16.v

/**
 * 16-bit multiplexor: 
 * for i = 0..15 out[i] = a[i] if sel == 0 
 *                        b[i] if sel == 1
 */
`default_nettype none

module Mux16(
	input [15:0] a,
	input [15:0] b,
   	input sel,
	output [15:0] out
);

// your implementation comes here:




endmodule
